ScourgeNest/E-Book-Reader-OpenSource/Images/E-Book Reader_Back.png

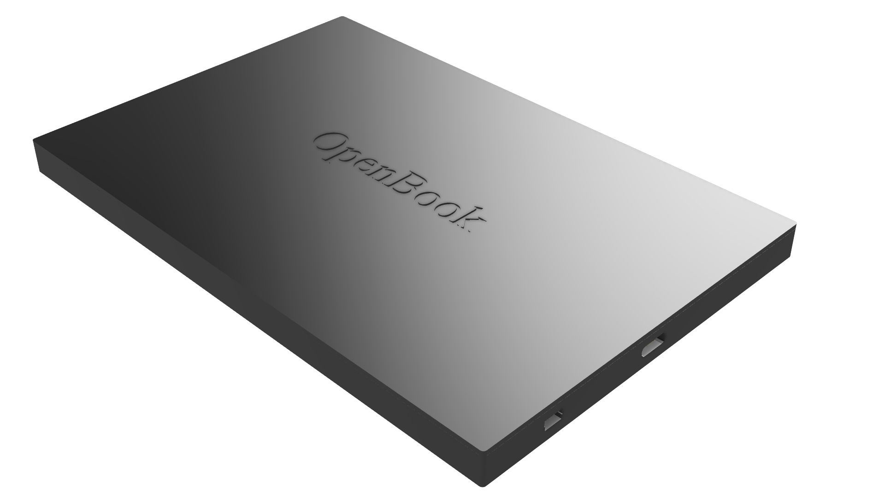
Images/E-Book Reader_Back.png
