ScourgeNest/E-Book-Reader-OpenSource/Images/Exploded_View.png

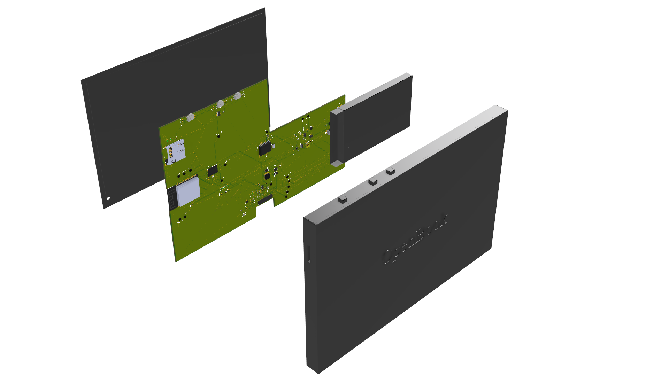
Images/Exploded_View.png
